MakerM0/MagiClick/documents/images/20230217_151108.jpg

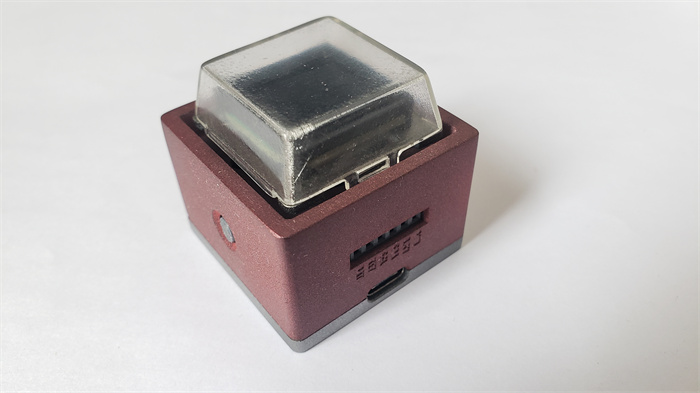
documents/images/20230217_151108.jpg
