MakerM0/MagiClick/documents/images/20230217_151208.jpg

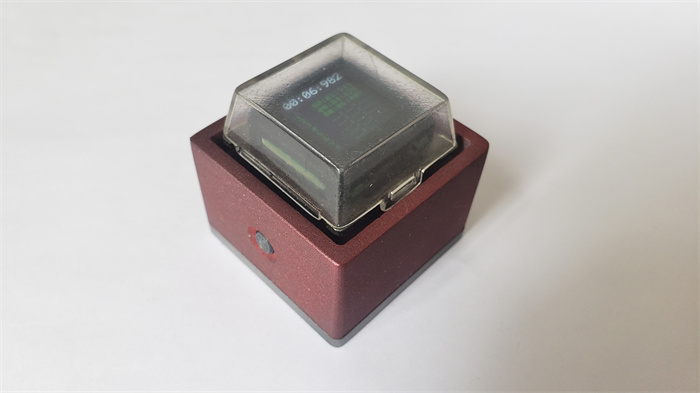
documents/images/20230217_151208.jpg
