MakerM0/MagiClick/documents/images/20230217_151217.jpg

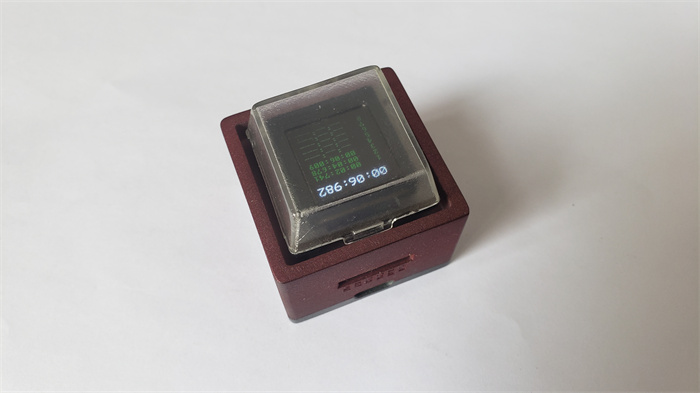
documents/images/20230217_151217.jpg
