MakerM0/MagiClick/firmware/firmware_wch583/drivers/Button2/Button2.cpp

/////////////////////////////////////////////////////////////////
/*
  Button2.cpp - Arduino Library to simplify working with buttons.
  Created by Lennart Hennigs.
*/
/////////////////////////////////////////////////////////////////

#include "Button2.h"

/////////////////////////////////////////////////////////////////
// initalize static counter

int Button2::_nextID = 0;

/////////////////////////////////////////////////////////////////
//  default contructor

Button2::Button2() {  
  pin = UNDEFINED_PIN;
  _setID();
}

/////////////////////////////////////////////////////////////////
// contructor

Button2::Button2(uint8_t attachTo, GPIOModeTypeDef buttonMode /* = INPUT_PULLUP */, bool activeLow /* = true */) {
  begin(attachTo, buttonMode, activeLow);
  _setID();
}

/////////////////////////////////////////////////////////////////



void Button2::begin(uint8_t attachTo, GPIOModeTypeDef buttonMode /* = INPUT_PULLUP */, bool activeLow /* = true */) {
  pin = attachTo;
  longclick_counter = 0;
  longclick_retriggerable = false;
  _pressedState = activeLow ? LOW : HIGH;
  if (attachTo != VIRTUAL_PIN) {
    pinMode(attachTo, buttonMode);
  }
  //  state = activeLow ? HIGH : LOW;
  state = _getState();
  prev_state = state ;
}

/////////////////////////////////////////////////////////////////

void Button2::setDebounceTime(unsigned int ms) {
  debounce_time_ms = ms;
}
    
/////////////////////////////////////////////////////////////////

void Button2::setLongClickTime(unsigned int ms) {
  longclick_time_ms = ms;
}

/////////////////////////////////////////////////////////////////

void Button2::setDoubleClickTime(unsigned int ms) {
  doubleclick_time_ms = ms;
}

/////////////////////////////////////////////////////////////////

unsigned int Button2::getDebounceTime() const {
  return debounce_time_ms;
}

/////////////////////////////////////////////////////////////////

unsigned int Button2::getLongClickTime() const {
  return longclick_time_ms;
}

/////////////////////////////////////////////////////////////////

unsigned int Button2::getDoubleClickTime() const {
  return doubleclick_time_ms;
}

/////////////////////////////////////////////////////////////////

uint8_t Button2::getPin() const {
  return pin;
}

/////////////////////////////////////////////////////////////////

void Button2::setButtonStateFunction(StateCallbackFunction f) {
  get_state_cb = f;
}

/////////////////////////////////////////////////////////////////

bool Button2::operator == (Button2 &rhs) {
  return (this == &rhs);    
}
      
/////////////////////////////////////////////////////////////////

void Button2::setChangedHandler(CallbackFunction f) {
  change_cb = f;
}
    
/////////////////////////////////////////////////////////////////

void Button2::setPressedHandler(CallbackFunction f) {
  pressed_cb = f; 
}

/////////////////////////////////////////////////////////////////

void Button2::setReleasedHandler(CallbackFunction f) {
  released_cb = f; 
}
        
/////////////////////////////////////////////////////////////////

void Button2::setClickHandler(CallbackFunction f) {
  click_cb = f;
}

/////////////////////////////////////////////////////////////////

void Button2::setTapHandler(CallbackFunction f) {
  tap_cb = f;
}

/////////////////////////////////////////////////////////////////

void Button2::setLongClickHandler(CallbackFunction f) {
  long_cb = f;
}

/////////////////////////////////////////////////////////////////

void Button2::setLongClickDetectedRetriggerable(bool retriggerable) {
  longclick_retriggerable = retriggerable;
}

/////////////////////////////////////////////////////////////////

void Button2::setLongClickDetectedHandler(CallbackFunction f) {
  longclick_detected_cb = f;
}

/////////////////////////////////////////////////////////////////

void Button2::setDoubleClickHandler(CallbackFunction f) {
  double_cb = f;
}

/////////////////////////////////////////////////////////////////

void Button2::setTripleClickHandler(CallbackFunction f) {
  triple_cb = f;
}

/////////////////////////////////////////////////////////////////

unsigned int Button2::wasPressedFor() const {
  return down_time_ms;
}

/////////////////////////////////////////////////////////////////

bool Button2::isPressed() const {
  return (state == _pressedState);
}

/////////////////////////////////////////////////////////////////

bool Button2::isPressedRaw() const {
  return (_getState() == _pressedState);
}

/////////////////////////////////////////////////////////////////

uint8_t Button2::getNumberOfClicks() const {
    return click_count;
}

/////////////////////////////////////////////////////////////////

clickType Button2::getType() const {
    return last_click_type;
}

/////////////////////////////////////////////////////////////////

int Button2::getID() const {
   return id;
 }

/////////////////////////////////////////////////////////////////

void Button2::setID(int newID) {
  id = newID;
 }

/////////////////////////////////////////////////////////////////

//char *Button2::clickToString(clickType type) const {
//  if (type == single_click) return "click";
//  if (type == long_click)   return "long click";
//  if (type == double_click) return "double click";
//  if (type == triple_click) return "triple click";
//  return "none";
// }

/////////////////////////////////////////////////////////////////

bool Button2::wasPressed() const {
  return was_pressed;
}

/////////////////////////////////////////////////////////////////

clickType Button2::read(bool keepState /* = false */) {
  if (keepState) {
    return last_click_type;
  }
  clickType res = last_click_type;
  last_click_type = empty;
  was_pressed = false;
  return res;
}

/////////////////////////////////////////////////////////////////

clickType Button2::wait(bool keepState /* = false */) {
  while(!wasPressed()) {
    loop();
  }
  return read(keepState);
}

/////////////////////////////////////////////////////////////////

void Button2::waitForClick(bool keepState /* = false */) {
  do {
    while(!wasPressed()) {
      loop();
    }
  } while(read() != single_click);
}

/////////////////////////////////////////////////////////////////

void Button2::waitForDouble(bool keepState  /* = false */) {
  do {
    while(!wasPressed()) {
      loop();
    }
  } while(read() != double_click);
}

/////////////////////////////////////////////////////////////////

void Button2::waitForTriple(bool keepState /* = false */) {
  do {
    while(!wasPressed()) {
      loop();
    }
  } while(read() != triple_click);
}

/////////////////////////////////////////////////////////////////

void Button2::waitForLong(bool keepState  /* = false */) {
  do {
    while(!wasPressed()) {
      loop();
    }
  } while(read() != long_click);
}

/////////////////////////////////////////////////////////////////

void Button2::reset() {
  pin = UNDEFINED_PIN;
  click_count = 0;
  last_click_type = empty;
  down_time_ms = 0;

  pressed_triggered = false;
  longclick_detected = false;
  longclick_reported = false;
  longclick_counter = 0;

  pressed_cb = NULL;
  released_cb = NULL;
  change_cb = NULL;
  tap_cb = NULL;
  click_cb = NULL;
  long_cb = NULL;
  longclick_detected_cb = NULL;
  double_cb = NULL;
  triple_cb = NULL;
}

/////////////////////////////////////////////////////////////////

void Button2::loop() {
  if (pin == UNDEFINED_PIN) return;
  prev_state = state;
  state = _getState();

  if (state == _pressedState) {
    _handlePress(millis());
  } else {
    _handleRelease(millis());
  }
}

/////////////////////////////////////////////////////////////////

void Button2::_handlePress(long now) {
  // is it pressed now?
  if (prev_state != _pressedState) {
    _pressedNow(now);
    return;
  }
  // is it pressed for a while?
  if (!pressed_triggered) {
    if (now - down_ms >= debounce_time_ms) {
      pressed_triggered = true;
      _validKeypress();
    }
  }
  // only check for longpress on the first click
  if (click_count == 1) {
    _checkForLongClick(now);
  }
}

/////////////////////////////////////////////////////////////////

void Button2::_setID() {
  id = _nextID;
  _nextID++;
}

/////////////////////////////////////////////////////////////////

void Button2::_handleRelease(long now) {
  // is it released right now?
  if (prev_state == _pressedState) {
    _releasedNow(now);
    return;
  } 
  // report click after double click time has passed
  if (now - click_ms > doubleclick_time_ms) {
    if (click_count > 0) {
      _reportClicks();
    }
  }
}

/////////////////////////////////////////////////////////////////

void Button2::_pressedNow(long now) {
    down_ms = now;
    pressed_triggered = false;
    click_ms = down_ms;
}

/////////////////////////////////////////////////////////////////

void Button2::_validKeypress() {
  click_count++;
  if (change_cb != NULL) change_cb (*this);      
  if (pressed_cb != NULL) pressed_cb (*this);
}

/////////////////////////////////////////////////////////////////

void Button2::_checkForLongClick(long now) {
  if (longclick_detected_cb != NULL) {
    if (longclick_reported) return;      
    // has the longclick_ms period has been exceeded?    
    if (now - down_ms >= (longclick_time_ms * (longclick_counter + 1))) {
      // report mutliple?
      if (!longclick_retriggerable) {
        longclick_reported = true;
      }
      longclick_counter++;
      longclick_detected_cb(*this);
      longclick_detected = true;
    }
  }
}

/////////////////////////////////////////////////////////////////

uint8_t Button2::getLongClickCount() const {
  return longclick_counter;
}

/////////////////////////////////////////////////////////////////

void Button2::_reportClicks() {
  switch (click_count) {
    case 1:
      if (longclick_detected) {
          last_click_type = long_click;
          if (long_cb != NULL) long_cb (*this);
          longclick_counter = 0;
      } else {
        last_click_type = single_click;
        if (click_cb != NULL) click_cb (*this);
        was_pressed = true;
      }
      break;

    case 2: 
      last_click_type = double_click;
      if (double_cb != NULL) double_cb (*this);
      was_pressed = true;
      break;

    case 3:
    // detect x-clicks as triple
    default: 
      last_click_type = triple_click;
      if (triple_cb != NULL) triple_cb (*this);
      was_pressed = true;
      break;
    }
    click_count = 0;
    click_ms = 0;
    longclick_detected = false;
    longclick_reported = false;

}

/////////////////////////////////////////////////////////////////

void Button2::_releasedNow(long now) {
  down_time_ms = now - down_ms;
  // is it beyond debounce time?
  if (down_time_ms >= debounce_time_ms) {
    last_click_type = single_click;
    // trigger release        
    if (change_cb != NULL) change_cb (*this);
    if (released_cb != NULL) released_cb (*this);
    // trigger tap
    if (tap_cb != NULL) tap_cb (*this);        
    // was it a longclick? (preceeds single / double / triple clicks)
    if (down_time_ms >= longclick_time_ms) {
      longclick_detected = true;
    }
  }
}

/////////////////////////////////////////////////////////////////

uint8_t Button2::_getState() const {
  if (get_state_cb != NULL) {
    return get_state_cb();
  } else {
    return digitalRead(pin);
  }
}

/////////////////////////////////////////////////////////////////
