MakerM0/MagiClick/firmware/firmware_wch583/subsys/HAL/MCU.c

/********************************** (C) COPYRIGHT *******************************
 * File Name          : MCU.c
 * Author             : WCH
 * Version            : V1.1
 * Date               : 2019/11/05
 * Description        : 硬件任务处理函数及BLE和硬件初始化
 *******************************************************************************/

/******************************************************************************/
/* 头文件包含 */
#include "CH58x_common.h"
#include "HAL.h"
#include "LCD_show/show_task.h"

#include "sensor/sensor_task.h"
#include "ISP583.h"
tmosTaskID halTaskID;

/*******************************************************************************
 * @fn          Lib_Calibration_LSI
 *
 * @brief       内部32k校准
 *
 * input parameters
 *
 * @param       None.
 *
 * output parameters
 *
 * @param       None.
 *
 * @return      None.
 */
void Lib_Calibration_LSI(void) {
    Calibration_LSI(Level_64);
}

#if (defined (BLE_SNV)) && (BLE_SNV == TRUE)
/*******************************************************************************
 * @fn          Lib_Read_Flash
 *
 * @brief       Lib 操作Flash回调
 *
 * input parameters
 *
 * @param       addr.
 * @param       num.
 * @param       pBuf.
 *
 * output parameters
 *
 * @param       None.
 *
 * @return      None.
 */
u32 Lib_Read_Flash(u32 addr, u32 num, u32 *pBuf) {
    EEPROM_READ(addr, pBuf, num * 4);
    return 0;
}

/*******************************************************************************
 * @fn          Lib_Write_Flash
 *
 * @brief       Lib 操作Flash回调
 *
 * input parameters
 *
 * @param       addr.
 * @param       num.
 * @param       pBuf.
 *
 * output parameters
 *
 * @param       None.
 *
 * @return      None.
 */
u32 Lib_Write_Flash(u32 addr, u32 num, u32 *pBuf) {
    EEPROM_ERASE(addr, EEPROM_PAGE_SIZE*2);
    EEPROM_WRITE(addr, pBuf, num * 4);
    return 0;
}
#endif

/*******************************************************************************
 * @fn          CH58X_BLEInit
 *
 * @brief       BLE 库初始化
 *
 * input parameters
 *
 * @param       None.
 *
 * output parameters
 *
 * @param       None.
 *
 * @return      None.
 */
void CH58X_BLEInit(void) {
    uint8 i;
    bleConfig_t cfg;
    if (tmos_memcmp(VER_LIB, VER_FILE, strlen( VER_FILE)) == FALSE) {
        PRINT("head file error...\n");
        while( 1 )
        ;
    }
//  SysTick_Config( SysTick_LOAD_RELOAD_Msk );
//  PFIC_DisableIRQ( SysTick_IRQn );

    tmos_memset(&cfg, 0, sizeof(bleConfig_t));
    cfg.MEMAddr = (u32) MEM_BUF;
    cfg.MEMLen = (u32) BLE_MEMHEAP_SIZE;
    cfg.BufMaxLen = (u32) BLE_BUFF_MAX_LEN;
    cfg.BufNumber = (u32) BLE_BUFF_NUM;
    cfg.TxNumEvent = (u32) BLE_TX_NUM_EVENT;
    cfg.TxPower = (u32) BLE_TX_POWER;
#if (defined (BLE_SNV)) && (BLE_SNV == TRUE)
    FLASH_ROM_LOCK(0);                    // 解锁flash
    cfg.SNVAddr = (u32) BLE_SNV_ADDR;
    cfg.readFlashCB = Lib_Read_Flash;
    cfg.writeFlashCB = Lib_Write_Flash;
#endif
#if( CLK_OSC32K )
    cfg.SelRTCClock = ( u32 ) CLK_OSC32K;
#endif
    cfg.ConnectNumber = ( PERIPHERAL_MAX_CONNECTION & 3)
            | ( CENTRAL_MAX_CONNECTION << 2);
    cfg.srandCB = SYS_GetSysTickCnt;
#if (defined TEM_SAMPLE)  && (TEM_SAMPLE == TRUE)
    cfg.tsCB = HAL_GetInterTempValue;    // 根据温度变化校准RF和内部RC( 大于7摄氏度 )
#if( CLK_OSC32K )
            cfg.rcCB = Lib_Calibration_LSI;    // 内部32K时钟校准
#endif
#endif
#if (defined (HAL_SLEEP)) && (HAL_SLEEP == TRUE)
    cfg.WakeUpTime = WAKE_UP_RTC_MAX_TIME;
    cfg.sleepCB = CH58X_LowPower;    // 启用睡眠
#endif
#if (defined (BLE_MAC)) && (BLE_MAC == TRUE)
    for (i = 0; i < 6; i++)
        cfg.MacAddr[i] = MacAddr[5 - i];
#else
    {
        uint8 MacAddr[6];
        GetMACAddress( MacAddr );
        for(i=0;i<6;i++) cfg.MacAddr[i] = MacAddr[i];    // 使用芯片mac地址
    }
#endif
    if (!cfg.MEMAddr || cfg.MEMLen < 4 * 1024)
        while( 1 )
        ;
    i = BLE_LibInit(&cfg);
    if (i) {
        PRINT("LIB init error code: %x ...\n", i);
        while( 1 )
        ;
    }
}

static void HAL_ProcessTMOSMsg(tmos_event_hdr_t *pMsg) {
    switch (pMsg->event) {
    case KEY_CHANGE: {
        keyChange_t *msg = (keyChange_t *) pMsg;
        static uint8_t func = 0;
        if (msg->keys == KEY1_DOWN) {
            /*震动马达*/

        }
    }
        break;

    default:
        break;
    }
}

/*******************************************************************************
 * @fn          HAL_ProcessEvent
 *
 * @brief       硬件层事务处理
 *
 * input parameters
 *
 * @param       task_id.
 * @param       events.
 *
 * output parameters
 *
 * @param       events.
 *
 * @return      None.
 */
tmosEvents HAL_ProcessEvent(tmosTaskID task_id, tmosEvents events) {
    uint8 * msgPtr;

    if (events & SYS_EVENT_MSG) {  // 处理HAL层消息，调用tmos_msg_receive读取消息，处理完成后删除消息。
        msgPtr = tmos_msg_receive(task_id);
        if (msgPtr) {
            HAL_ProcessTMOSMsg((tmos_event_hdr_t *) msgPtr);
            /* De-allocate */
            tmos_msg_deallocate(msgPtr);
        }
        return events ^ SYS_EVENT_MSG;
    }

    if (events & HAL_TIME_EVENT) {
        timestamp++;
        mytime = localtime(&timestamp);
        return events ^ HAL_TIME_EVENT;
    }

    if (events & LED_BLINK_EVENT) {
#if (defined HAL_LED) && (HAL_LED == TRUE)
        HalLedUpdate( );
#endif // HAL_LED
        return events ^ LED_BLINK_EVENT;
    }
    if (events & HAL_KEY_EVENT) {
#if (defined HAL_KEY) && (HAL_KEY == TRUE)
        HAL_KeyPoll(); /* Check for keys */
        tmos_start_task(halTaskID, HAL_KEY_EVENT, MS1_TO_SYSTEM_TIME(10));
        return events ^ HAL_KEY_EVENT;
#endif
    }
    if (events & HAL_REG_INIT_EVENT) {
#if (defined BLE_CALIBRATION_ENABLE) && (BLE_CALIBRATION_ENABLE == TRUE)    // 校准任务，单次校准耗时小于10ms
        BLE_RegInit();    // 校准RF
#if( CLK_OSC32K )
        Lib_Calibration_LSI();    // 校准内部RC
#endif
        tmos_start_task(halTaskID, HAL_REG_INIT_EVENT,
                MS1_TO_SYSTEM_TIME(BLE_CALIBRATION_PERIOD));
        return events ^ HAL_REG_INIT_EVENT;
#endif
    }

    if (events & HAL_SHUTDONW_EVENT) {
        LOG_INFO("Shut down!");
#if( DEBUG == Debug_UART1 )  // 使用其他串口输出打印信息需要修改这行代码
        while( ( R8_UART1_LSR & RB_LSR_TX_ALL_EMP ) == 0 )
        __nop();
#endif
        LowPower_Shutdown(0);

        CODE_UNREACHABLE;

        return events ^ HAL_SHUTDONW_EVENT;
    }

    if (events & HAL_TEST_EVENT) {
        PRINT("*\n");
        tmos_start_task(halTaskID, HAL_TEST_EVENT, MS1_TO_SYSTEM_TIME(1000));
        return events ^ HAL_TEST_EVENT;
    }
    return 0;
}

/*******************************************************************************
 * @fn          HAL_Init
 *
 * @brief       硬件初始化
 *
 * input parameters
 *
 * @param       None.
 *
 * output parameters
 *
 * @param       None.
 *
 * @return      None.
 */
void HAL_Init() {
    halTaskID = TMOS_ProcessEventRegister(HAL_ProcessEvent);
    HAL_TimeInit();
    tmos_start_reload_task(halTaskID, HAL_TIME_EVENT, MS1_TO_SYSTEM_TIME(1000));
#if (defined HAL_SLEEP) && (HAL_SLEEP == TRUE)
    HAL_SleepInit();
#endif
#if (defined HAL_LED) && (HAL_LED == TRUE)
    HAL_LedInit( );
#endif
#if (defined HAL_ADC) && (HAL_ADC == TRUE)
    HalAdcInit( );
#endif
#if (defined HAL_KEY) && (HAL_KEY == TRUE)
    HAL_KeyInit();
#endif
#if ( defined BLE_CALIBRATION_ENABLE ) && ( BLE_CALIBRATION_ENABLE == TRUE )
    tmos_start_task(halTaskID, HAL_REG_INIT_EVENT,
            MS1_TO_SYSTEM_TIME(BLE_CALIBRATION_PERIOD));  // 添加校准任务，单次校准耗时小于10ms
#endif
//  tmos_start_task( halTaskID, HAL_TEST_EVENT, 1600 );    // 添加一个测试任务
}

/*******************************************************************************
 * @fn          HAL_GetInterTempValue
 *
 * @brief       如果使用了ADC中断采样，需在此函数中暂时屏蔽中断.
 *
 * input parameters
 *
 * @param       None.
 *
 * output parameters
 *
 * @param       None.
 *
 * @return      None.
 */
uint16 HAL_GetInterTempValue(void) {
    uint8 sensor, channel, config, tkey_cfg;
    uint16 adc_data;

    tkey_cfg = R8_TKEY_CFG;
    sensor = R8_TEM_SENSOR;
    channel = R8_ADC_CHANNEL;
    config = R8_ADC_CFG;
    ADC_InterTSSampInit();
    R8_ADC_CONVERT |= RB_ADC_START;
    while( R8_ADC_CONVERT & RB_ADC_START )
    ;
    adc_data = R16_ADC_DATA;
    R8_TEM_SENSOR = sensor;
    R8_ADC_CHANNEL = channel;
    R8_ADC_CFG = config;
    R8_TKEY_CFG = tkey_cfg;
    return (adc_data);
}

uint8 OnBoard_SendMsg(uint8_t registeredTaskID, uint8 event, uint8 state,
        void *data) {
    SendMSG_t *msgPtr;

    if (registeredTaskID != TASK_NO_TASK) {
        // Send the address to the task
        msgPtr = (SendMSG_t *) tmos_msg_allocate(sizeof(SendMSG_t));
        if (msgPtr) {
            msgPtr->hdr.event = event;
            msgPtr->hdr.status = state;
            msgPtr->pData = data;
            tmos_msg_send(registeredTaskID, (uint8 *) msgPtr);

        }
        return ( SUCCESS);
    } else {
        return ( FAILURE);
    }
}

/******************************** endfile @ mcu ******************************/
