MakerM0/MagiClick/firmware/firmware_wch583/subsys/LCD_show/pages/pages.h

#ifndef __PAGES_H
#define __PAGES_H

#include "LCD_show/manager/manager.h"
#include "LCD_show/show_task.h"
#include "HAL/HAL.h"

extern page_t page_main;

extern page_t *pages[];
void switchpages();
#endif
