MakerM0/MagiClick/firmware/firmware_wch583/subsys/LCD_show/UGUI/ugui_fonts.h

#ifndef __UGUI_FONTS_DATA_H
#define __UGUI_FONTS_DATA_H

/* -------------------------------------------------------------------------------- */
/* -- µGUI FONTS                                                                 -- */
/* -- Source: http://www.mikrocontroller.net/user/show/benedikt                  -- */
/* -------------------------------------------------------------------------------- */
#include "ugui.h"
/*
  Old fonts converted to new structure. They use Code Page 850 encoding. UTF-8 can be disabled if only these fonts are being used.
  https://en.wikipedia.org/wiki/Code_page_850
*/

#ifdef UGUI_USE_FONT_4X16
extern UG_FONT FONT_4X6[];
#endif

#ifdef UGUI_USE_FONT_5X8
extern UG_FONT FONT_5X8[];
#endif

#ifdef UGUI_USE_FONT_5X12
extern UG_FONT FONT_5X12[];
#endif

#ifdef UGUI_USE_FONT_6X8
extern UG_FONT FONT_6X8[];
#endif

#ifdef UGUI_USE_FONT_6X10
extern UG_FONT FONT_6X10[];
#endif

#ifdef UGUI_USE_FONT_7X12
extern UG_FONT FONT_7X12[];
#endif

#ifdef UGUI_USE_FONT_8X8
extern UG_FONT FONT_8X8[];
#endif

#ifdef UGUI_USE_FONT_8X12
extern UG_FONT FONT_8X12[];
#endif

#ifdef UGUI_USE_FONT_8X12_CYRILLIC
extern UG_FONT FONT_8X12_CYRILLIC[];
#endif

#ifdef UGUI_USE_FONT_10X16
extern UG_FONT FONT_10X16[];
#endif

#ifdef UGUI_USE_FONT_12X16
extern UG_FONT FONT_12X16[];
#endif

#ifdef UGUI_USE_FONT_12X20
extern UG_FONT FONT_12X20[];
#endif

#ifdef UGUI_USE_FONT_16X26
extern UG_FONT FONT_16X26[];
#endif

#ifdef UGUI_USE_FONT_22X36
extern UG_FONT FONT_22X36[];
#endif

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
#ifdef UGUI_USE_FONT_arial_45X52_CYRILLIC
extern UG_FONT FONT_arial_45X52_CYRILLIC[];
#endif
#ifdef UGUI_USE_FONT_arial_49X57
extern UG_FONT FONT_arial_49X57[];
#endif
#ifdef UGUI_USE_FONT_arial_49X57_CYRILLIC
extern UG_FONT FONT_arial_49X57_CYRILLIC[];
#endif



#endif // __UGUI_FONTS_DATA_H
