MakerM0/MagiClick/firmware/firmware_wch583/subsys/LCD_show/GC9107/lcd.h

#ifndef __LCD_H
#define __LCD_H		
#include "CH58x_common.h"

typedef  uint16_t u16;
typedef  uint8_t u8;
typedef  uint32_t u32;




void LCD_Fill(u16 xsta,u16 ysta,u16 xend,u16 yend,u16 color);//指定区域填充颜色
void LCD_DrawPoint(u16 x,u16 y,u16 color);//在指定位置画一个点
void LCD_DrawLine(u16 x1,u16 y1,u16 x2,u16 y2,u16 color);//在指定位置画一条线
void LCD_DrawRectangle(u16 x1, u16 y1, u16 x2, u16 y2,u16 color);//在指定位置画一个矩形
void Draw_Circle(u16 x0,u16 y0,u8 r,u16 color);//在指定位置画一个圆

void LCD_ShowChinese(u16 x,u16 y,u8 *s,u16 fc,u16 bc,u8 sizey,u8 mode);//显示汉字串
void LCD_ShowChinese12x12(u16 x,u16 y,u8 *s,u16 fc,u16 bc,u8 sizey,u8 mode);//显示单个12x12汉字
void LCD_ShowChinese16x16(u16 x,u16 y,u8 *s,u16 fc,u16 bc,u8 sizey,u8 mode);//显示单个16x16汉字
void LCD_ShowChinese24x24(u16 x,u16 y,u8 *s,u16 fc,u16 bc,u8 sizey,u8 mode);//显示单个24x24汉字
void LCD_ShowChinese32x32(u16 x,u16 y,u8 *s,u16 fc,u16 bc,u8 sizey,u8 mode);//显示单个32x32汉字

void LCD_ShowChar(u16 x,u16 y,u8 num,u16 fc,u16 bc,u8 sizey,u8 mode);//显示一个字符
void LCD_ShowString(u16 x,u16 y,const u8 *p,u16 fc,u16 bc,u8 sizey,u8 mode);//显示字符串
u32 mypow(u8 m,u8 n);//求幂
void LCD_ShowIntNum0(uint16_t x,uint16_t y,uint16_t num,uint8_t len,uint16_t fc,uint16_t bc,uint8_t sizey, uint8_t mode);//显示整数变量
void LCD_ShowIntNum(uint16_t x,uint16_t y,uint16_t num,uint8_t len,uint16_t fc,uint16_t bc,uint8_t sizey, uint8_t mode);//显示整数变量
void LCD_ShowFloatNum1(uint16_t x,uint16_t y,float num,uint8_t len,uint16_t fc,uint16_t bc,uint8_t sizey);//显示两位小数变量

void LCD_ShowPicture(uint16_t x,uint16_t y,uint16_t length,uint16_t width,const uint8_t pic[]);//显示图片
void  LCD_DrawMonoImg(u16 x,u16 y, u16 width,u16 height,const uint8_t pic[],u16 color);
void  LCD_DrawMonoImgFast(u16 x,u16 y, u16 width,u16 height,const uint8_t pic[],u16 color,u16 bkcolor);
void  LCD_DrawMonoXBMFast(u16 x,u16 y, u16 width,u16 height,const uint8_t pic[],u16 color,u16 bkcolor);
//画笔颜色
#define WHITE         	 0xFFFF
#define BLACK         	 0x0000	  
#define BLUE           	 0x001F  
#define BRED             0XF81F
#define GRED 			       0XFFE0
#define GBLUE			       0X07FF
#define RED           	 0xF800
#define MAGENTA       	 0xF81F
#define GREEN         	 0x07E0
#define CYAN          	 0x7FFF
#define YELLOW        	 0xFFE0
#define BROWN 			     0XBC40 //棕色
#define BRRED 			     0XFC07 //棕红色
#define GRAY  			     0X8430 //灰色
#define DARKBLUE      	 0X01CF	//深蓝色
#define LIGHTBLUE      	 0X7D7C	//浅蓝色  
#define GRAYBLUE       	 0X5458 //灰蓝色
#define LIGHTGREEN     	 0X841F //浅绿色
#define LGRAY 			     0XC618 //浅灰色(PANNEL),窗体背景色
#define LGRAYBLUE        0XA651 //浅灰蓝色(中间层颜色)
#define LBBLUE           0X2B12 //浅棕蓝色(选择条目的反色)

#endif
